wes06/linobyte/Presentations/2018-05/Links/20tarja.jpg

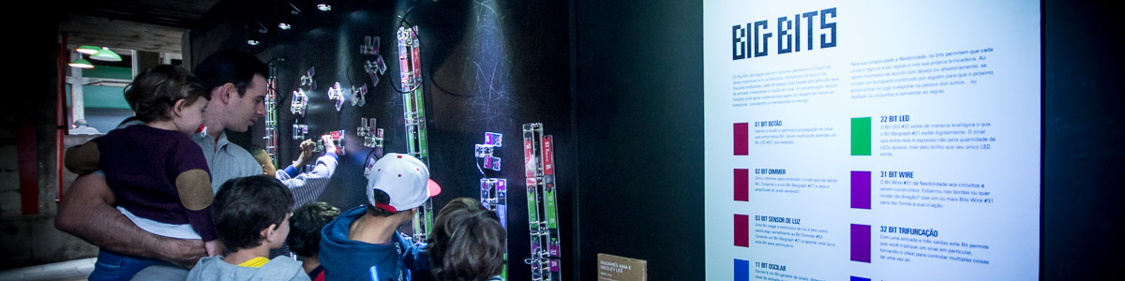
Presentations/2018-05/Links/20tarja.jpg
