wes06/linobyte/Presentations/2018-05/Links/Apollo_guidiance_computer_ferrit_core_memory.jpg

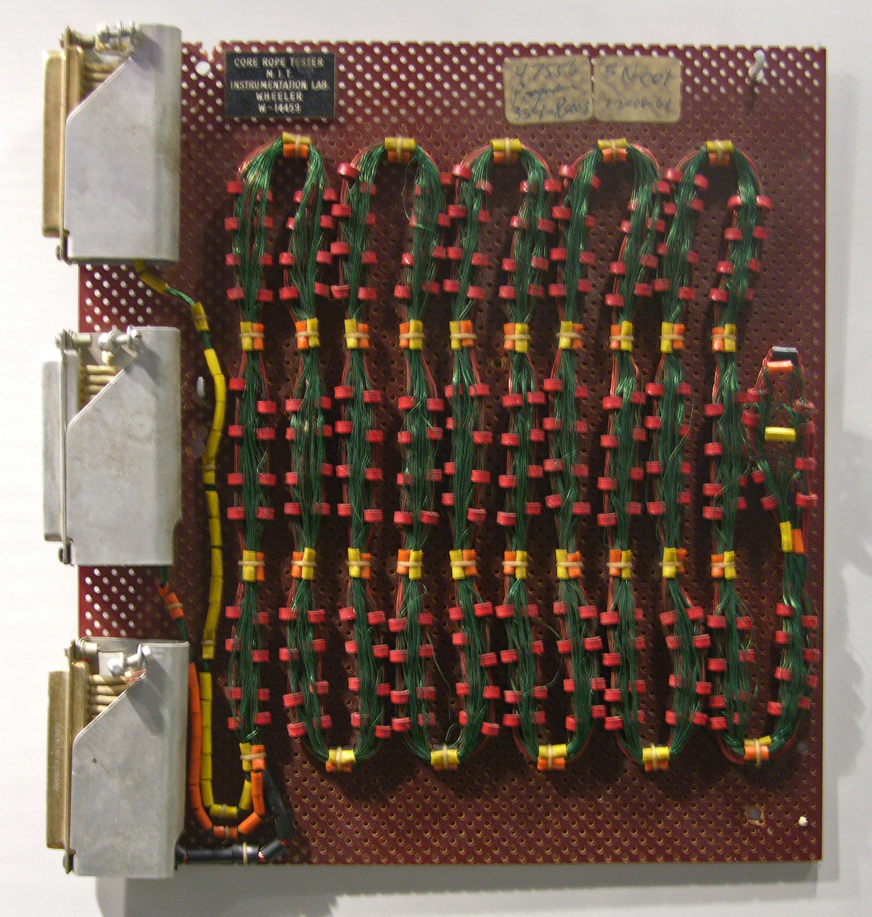
Presentations/2018-05/Links/Apollo_guidiance_computer_ferrit_core_memory.jpg
