wes06/linobyte/Presentations/2018-05/Links/decoding-rope-memory-from-agc-featured.png

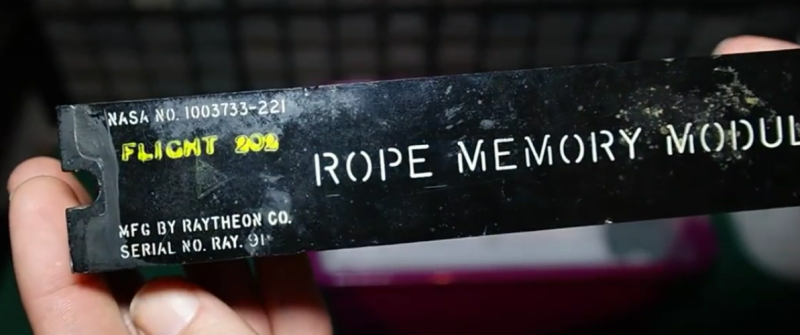
Presentations/2018-05/Links/decoding-rope-memory-from-agc-featured.png
