wes06/linobyte/Presentations/2018-05/Links/DSC_6382.JPG

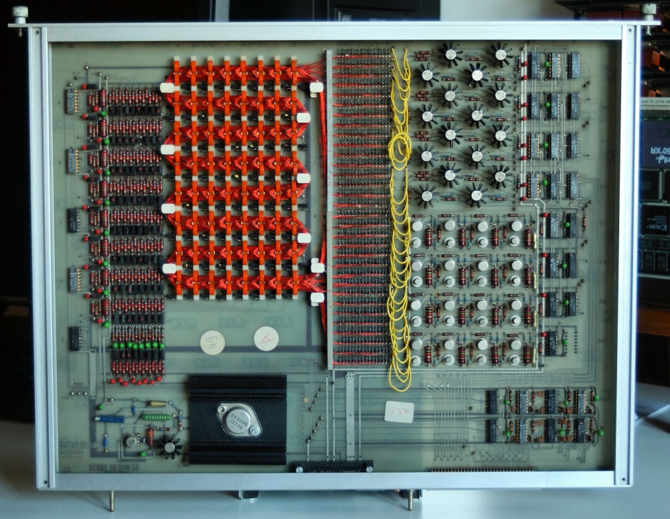
Presentations/2018-05/Links/DSC_6382.JPG
