wes06/linobyte/Presentations/2018-05/Links/e-ink-engadget.jpeg

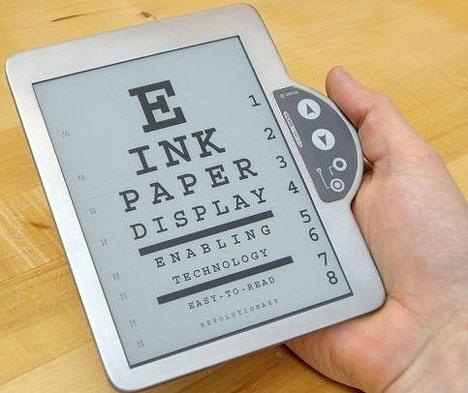
Presentations/2018-05/Links/e-ink-engadget.jpeg
