wes06/linobyte/Presentations/2018-05/Links/IMG_3371.jpg

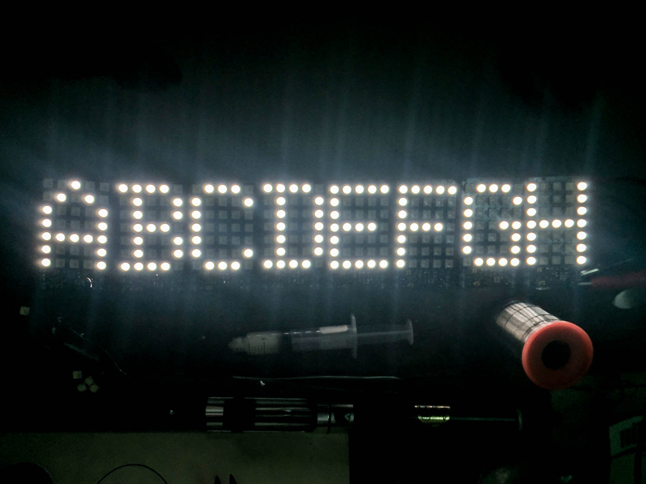
Presentations/2018-05/Links/IMG_3371.jpg
