wes06/linobyte/Presentations/2018-05/Links/s-l1600.jpg

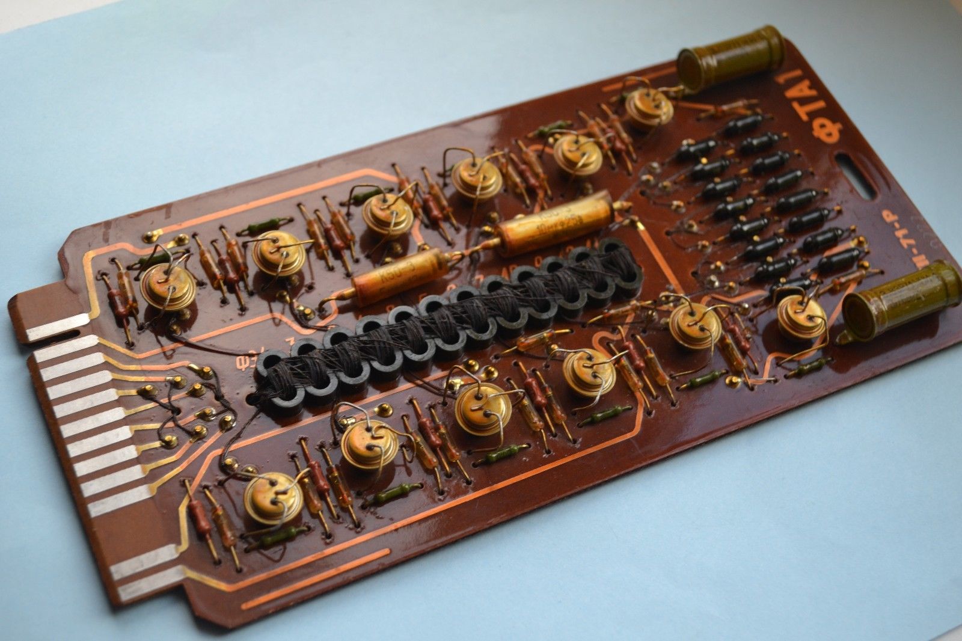
Presentations/2018-05/Links/s-l1600.jpg
