wes06/linobyte/Presentations/2018-05/Links/Screen Shot 2018-05-06 at 00.35.23.png

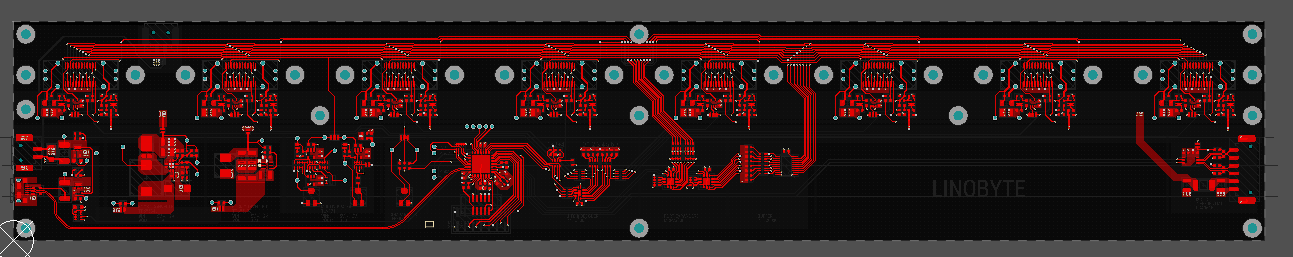
Presentations/2018-05/Links/Screen Shot 2018-05-06 at 00.35.23.png
