wes06/linobyte/Presentations/2018-05/Links/Screen Shot 2018-05-14 at 03.29.45.png

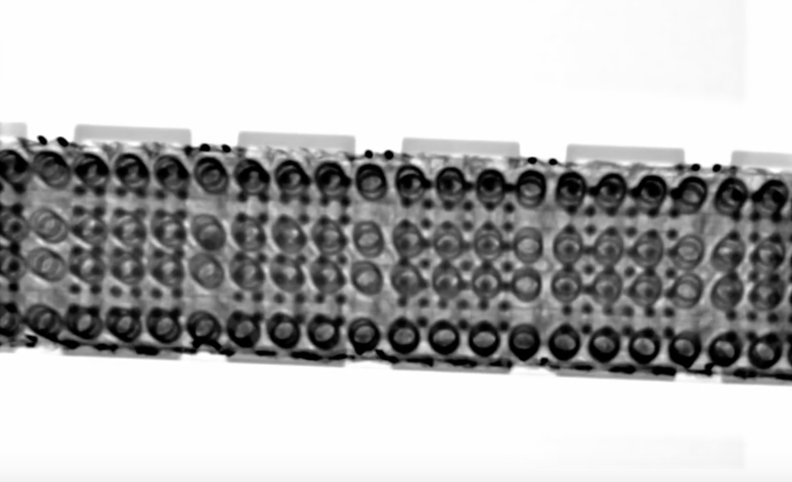
Presentations/2018-05/Links/Screen Shot 2018-05-14 at 03.29.45.png
