wes06/linobyte/Presentations/2018-05/Links/Screen Shot 2018-05-14 at 05.42.36.png

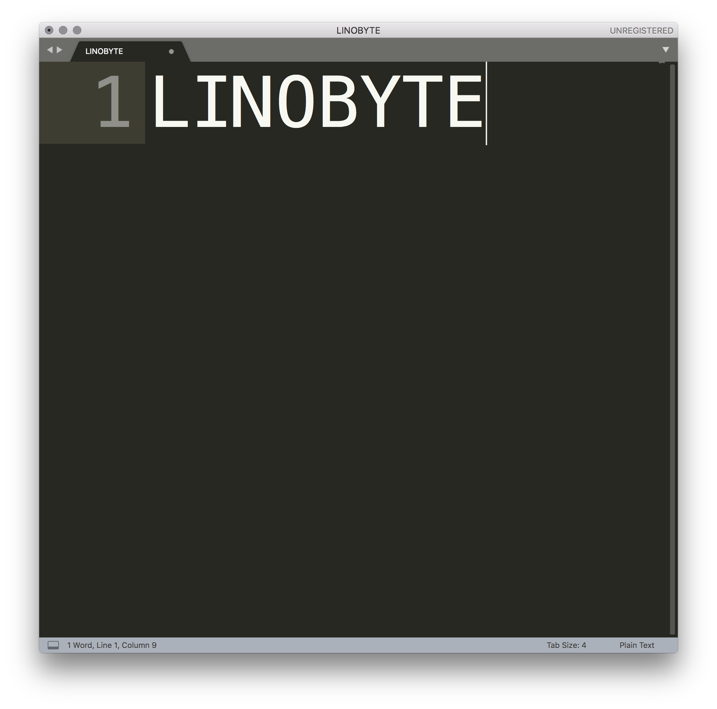
Presentations/2018-05/Links/Screen Shot 2018-05-14 at 05.42.36.png
