wes06/linobyte/Presentations/2018-05/Links/Screen Shot 2018-05-15 at 13.16.00.png

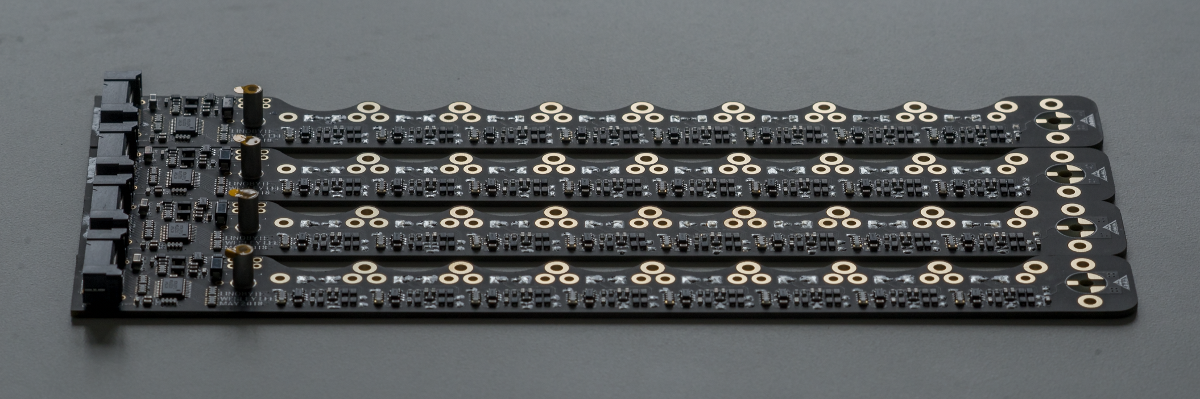
Presentations/2018-05/Links/Screen Shot 2018-05-15 at 13.16.00.png
