wes06/linobyte/Presentations/2018-05/Links/Screen Shot 2018-05-16 at 13.11.32.png

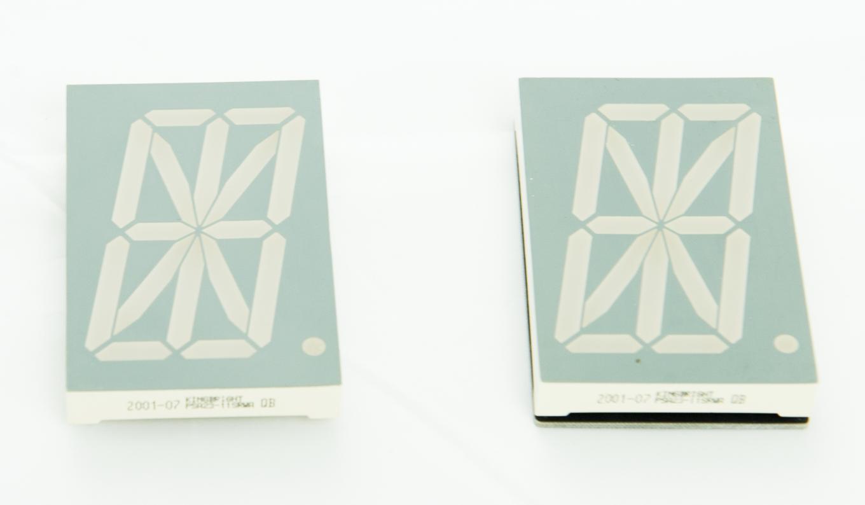
Presentations/2018-05/Links/Screen Shot 2018-05-16 at 13.11.32.png
