wes06/linobyte/Presentations/2018-05/Links/sketch2.png

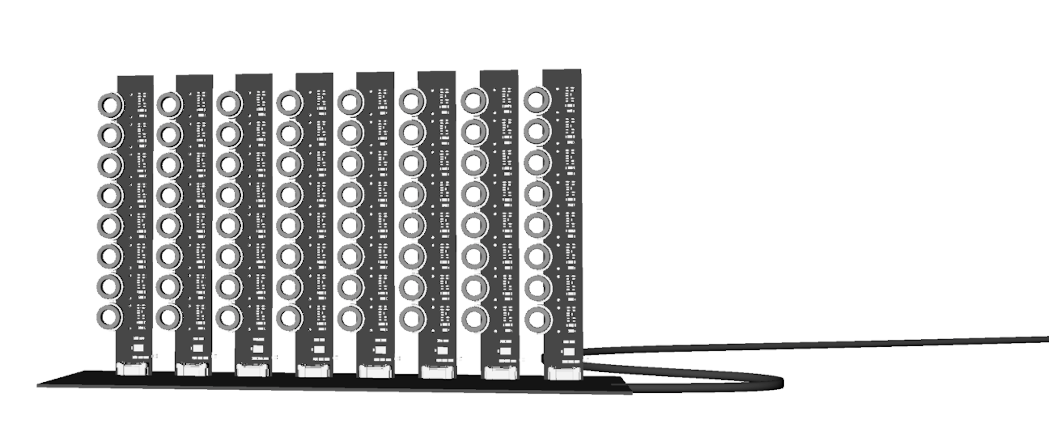
Presentations/2018-05/Links/sketch2.png
