wes06/linobyte/Firmware/Linobyte-Firmware/linobyte/ASCII-16Seg.h

/*
 *  Project     Segmented LED Display - ASCII Library
 *  @author     David Madison
 *  @link       github.com/dmadison/Segmented-LED-Display-ASCII
 *  @license    MIT - Copyright (c) 2017 David Madison
 *
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
 */
#include <cstdint>

const uint16_t SixteenSegmentASCII[95] = {
	0b0000000000000000, /* (space) */
	0b0000000000001100, /* ! */
	0b0000001000000100, /* " */
	0b1010101000111100, /* # */
	0b1010101010111011, /* $ */
	0b1110111010011001, /* % */
	0b1001001101110001, /* & */
	0b0000001000000000, /* ' */
	0b0001010000000000, /* ( */
	0b0100000100000000, /* ) */
	0b1111111100000000, /* * */
	0b1010101000000000, /* + */
	0b0100000000000000, /* , */
	0b1000100000000000, /* - */
	0b0001000000000000, /* . */
	0b0100010000000000, /* / */
	0b0100010011111111, /* 0 */ // 16
	0b0000010000001100, /* 1 */
	0b1000100001110111, /* 2 */
	0b0000100000111111, /* 3 */
	0b1000100010001100, /* 4 */
	0b1001000010110011, /* 5 */
	0b1000100011111011, /* 6 */
	0b0000000000001111, /* 7 */
	0b1000100011111111, /* 8 */
	0b1000100010111111, /* 9 */
	0b0010001000000000, /* : */
	0b0100001000000000, /* ; */
	0b1001010000000000, /* < */
	0b1000100000110000, /* = */
	0b0100100100000000, /* > */
	0b0010100000000111, /* ? */
	0b0000101011110111, /* @ */
	0b1000100011001111, /* A */ // 33
	0b0010101000111111, /* B */
	0b0000000011110011, /* C */
	0b0010001000111111, /* D */
	0b1000000011110011, /* E */
	0b1000000011000011, /* F */
	0b0000100011111011, /* G */
	0b1000100011001100, /* H */
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
};
